medo64/AuxPower1U/src/firmware/oled.h

#pragma once
#include <stdint.h>

void oled_init(void);
void oled_splash(void);

void oled_displayOn(void);
void oled_displayOff(void);

void oled_writeSummary(uint16_t voltage1, uint16_t current1, uint16_t voltage2, uint16_t current2, uint16_t voltage3, uint16_t current3, uint16_t voltage4, uint16_t current4, uint16_t voltage5, uint16_t current5, uint16_t temperature, uint8_t outputOnMask);
void oled_writeChannel(uint8_t channel, uint16_t voltage, uint16_t current, bool isOutputOff, uint8_t state, uint16_t ticks);

void oled_writeReset(uint8_t channel, uint16_t voltage, uint16_t current, uint16_t ticks);

void oled_writeTestVT(uint8_t index, uint16_t voltage, uint16_t temperature);
void oled_writeTestVC(uint8_t index, uint16_t voltage, uint16_t current);
